Charlotte-MEDI/Faceshields/prusaFaceShield/bottom_reinforcement_thickshield.stl

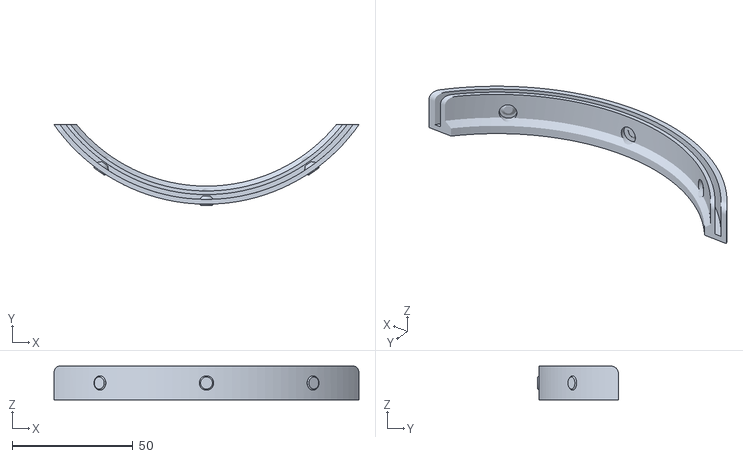
[picture p18: CAD file, 2020-03-23]
prusaFaceShield/bottom_reinforcement_thickshield.stl
126.4 x 33.5 x 14.0
