Charlotte-MEDI/Faceshields/prusaFaceShield/covid19_headband_rc2_2pcs.3mf

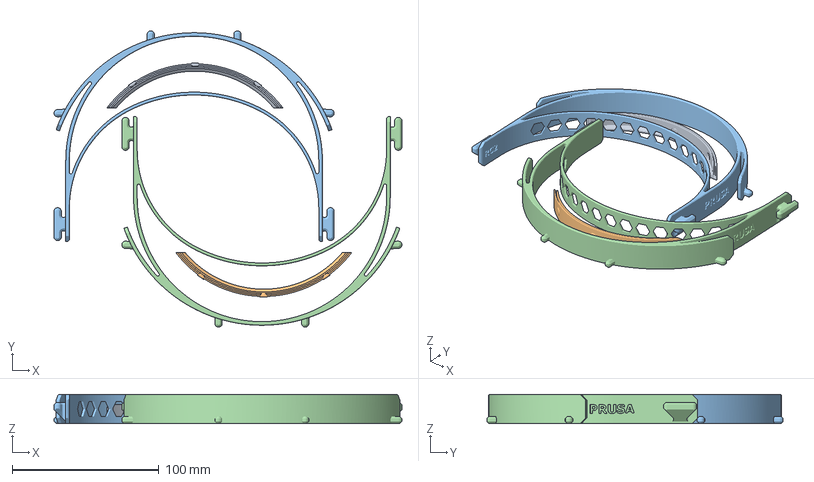
[picture p19: CAD file, 2020-03-22]
prusaFaceShield/covid19_headband_rc2_2pcs.3mf
237.2 x 202.0 x 20.0 mm
reinforcement_final.stl
COVID19_SHIELD_RC2.stl
