Charlotte-MEDI/Faceshields/prusaFaceShield/covid19_headband_rc2_1pcs.3mf

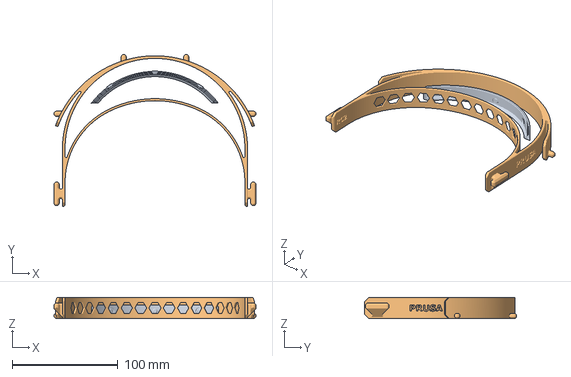
[picture p20: CAD file, 2020-03-22]
prusaFaceShield/covid19_headband_rc2_1pcs.3mf
191.0 x 143.8 x 20.0 mm
reinforcement_final.stl
COVID19_SHIELD_RC2.stl
