Charlotte-MEDI/Faceshields/prusaFaceShield/covid19-shield.3mf

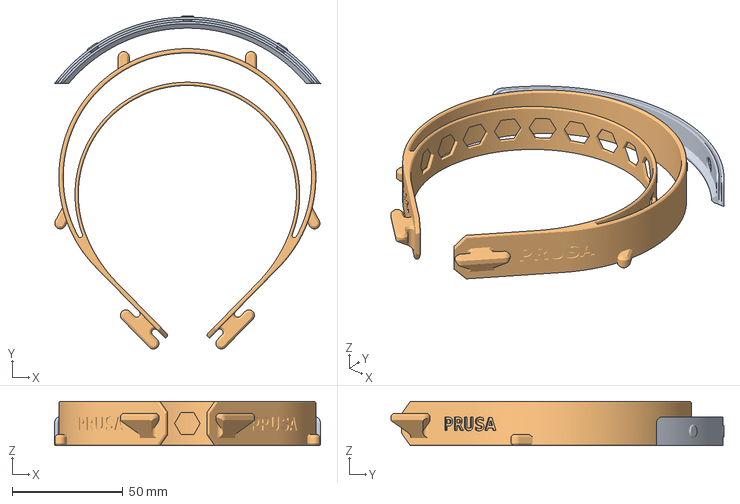
[picture p21: CAD file, 2020-03-22]
prusaFaceShield/covid19-shield.3mf
120.1 x 150.3 x 20.0 mm
reinforcement_final.stl
COVID19_SHILED_R1 (1).stl
