Charlotte-MEDI/Faceshields/prusaFaceShield/shield_final.dxf

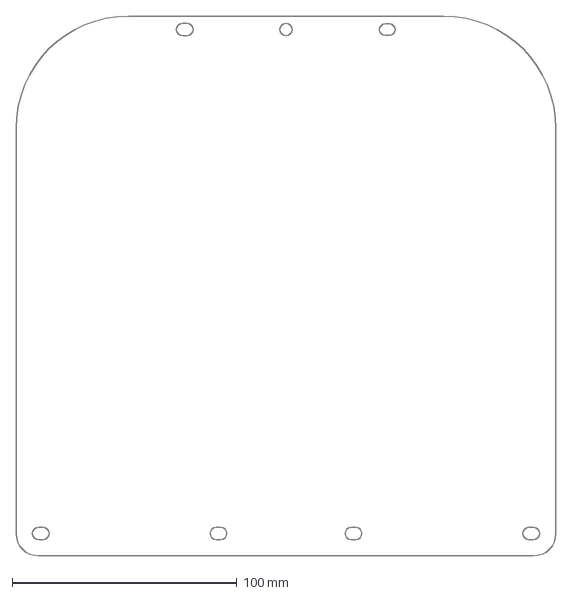
[picture p22: CAD file, 2020-03-21]
prusaFaceShield/shield_final.dxf
240.0 x 240.0 mm
